RR-CREATOR/GLARE/ARglassesFIRMWARE/src/utils/i2c_devices.c

#include "utils/i2c_devices.h"
#include "driver/i2c.h"

#define I2C_SCL 21
#define I2C_SDA 14

void i2c_devices_init(void) {
    i2c_config_t config = {
        .mode = I2C_MODE_MASTER,
        .sda_io_num = I2C_SDA,
        .sda_pullup_en = GPIO_PULLUP_ENABLE,
        .scl_io_num = I2C_SCL,
        .scl_pullup_en = GPIO_PULLUP_ENABLE,
        .master.clk_speed = 400000
    };
    i2c_param_config(I2C_NUM_0, &config);
    i2c_driver_install(I2C_NUM_0, config.mode, 0, 0, 0);
}
